Hans-Beerman/NodeCompressor/Photos/20200428_143928.jpg

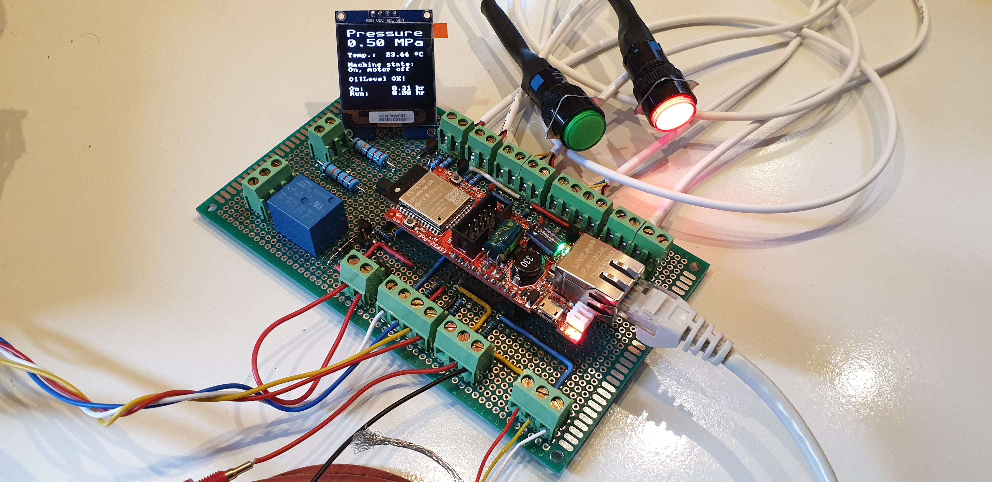
Photos/20200428_143928.jpg
