Hans-Beerman/NodeCompressor/Photos/20201005_140811.jpg

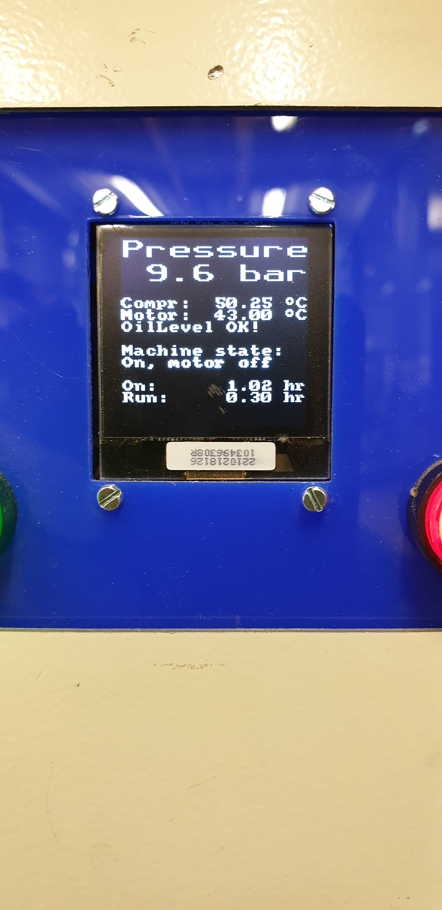
Photos/20201005_140811.jpg
