Hans-Beerman/NodeCompressor/Photos/20201005_140847.jpg

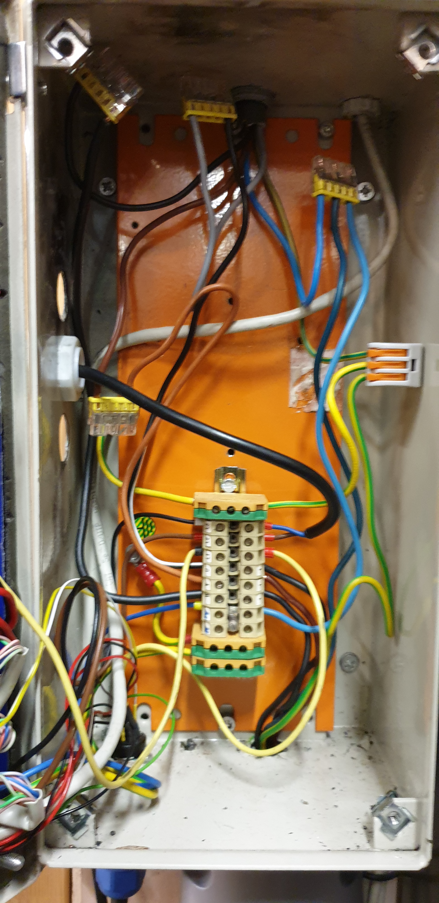
Photos/20201005_140847.jpg
