Hans-Beerman/NodeCompressor/Photos/20201005_140854.jpg

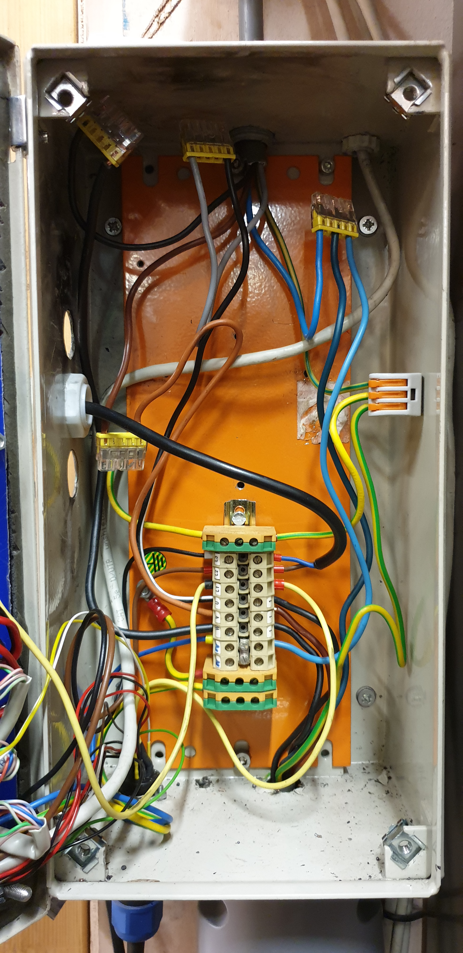
Photos/20201005_140854.jpg
