Hans-Beerman/NodeCompressor/Photos/20201005_140933.jpg

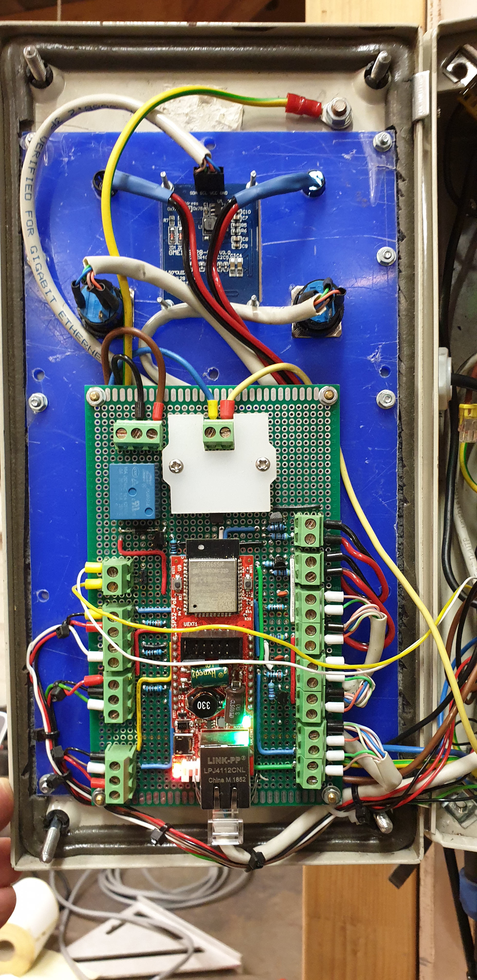
Photos/20201005_140933.jpg
