Hans-Beerman/NodeCompressor/Photos/20201005_141557.jpg

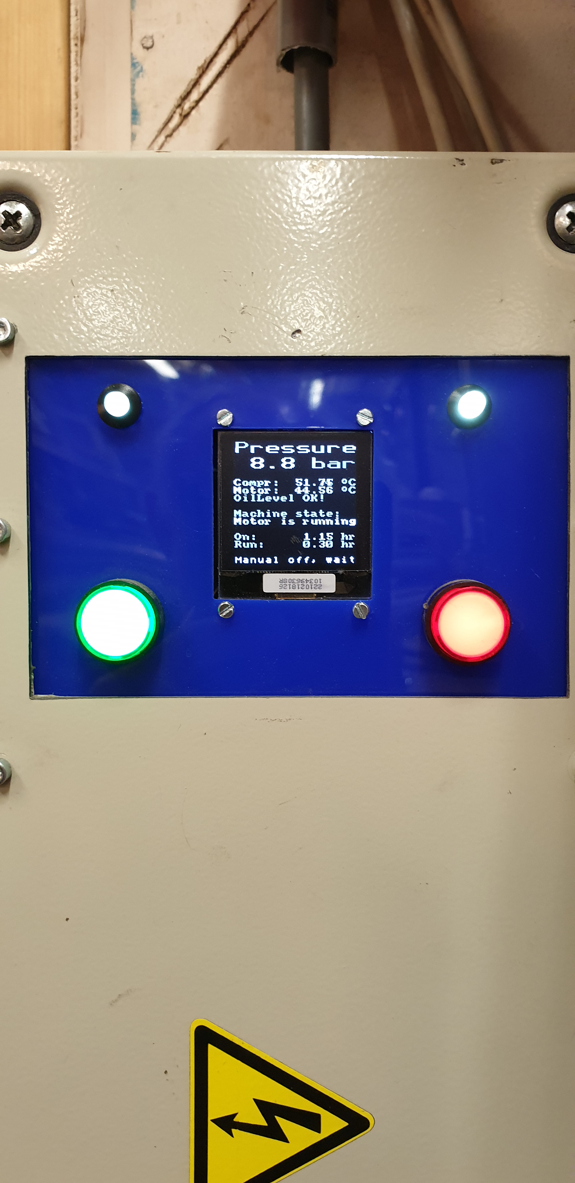
Photos/20201005_141557.jpg
