Hans-Beerman/NodeCompressor/KiCad files/CompressorNode/CompressorNode-F_Cu.pdf

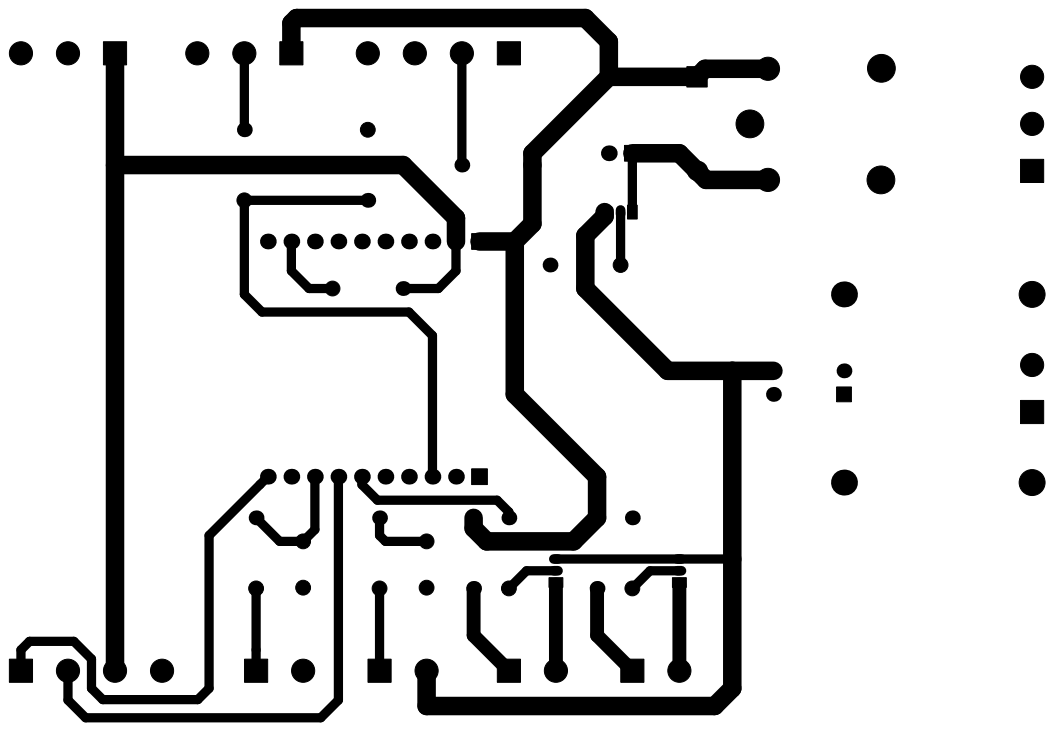
[picture p21: page 1]
