Hans-Beerman/NodeCompressor/KiCad files/CompressorNode/CompressorNode-F_SilkS.pdf

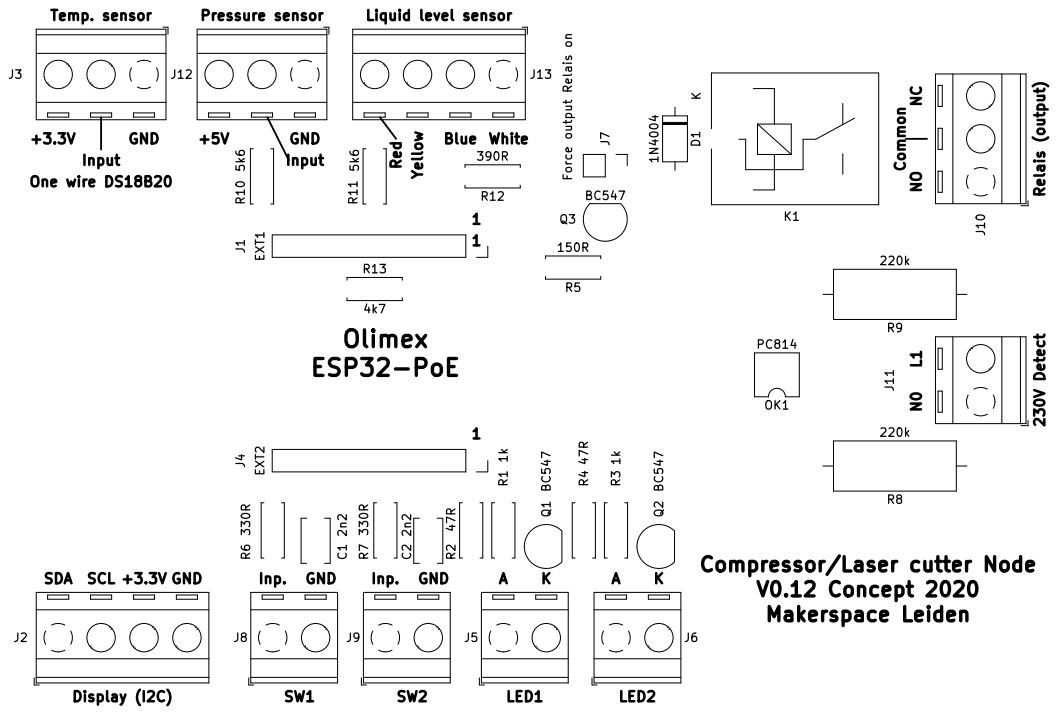
[picture p22: page 1]
